xchgeaxeax90/wisp-nametag/src_avr/animation.c

#include "animation.h"
#include <avr/interrupt.h>
#include <avr/io.h>

#include "animation_circle.inc"
#include "animation_breathe.inc"
#include "animation_wave.inc"
#include "animation_blink.inc"
#include "animation_twinkle.inc"
#include "animation_on.inc"

const __flash animation_data_t animation_off[] = {
    {{ 0, 0, 0, 0, 0, 0, 0, 0, 0, 0}, .timeout = 10}
};

const __flash animation_data_t* animation_array[] = {
    animation_circle,
    animation_twinkle,
    animation_breathe,
    animation_wave,
    animation_blink,
    animation_on,
    animation_off
};
const uint8_t max_animation_select = 5;


const __flash uint8_t animation_sizes[] = {
    sizeof(animation_circle)/sizeof(animation_circle[0]),
    sizeof(animation_twinkle)/sizeof(animation_twinkle[0]),
    sizeof(animation_breathe)/sizeof(animation_breathe[0]),
    sizeof(animation_wave)/sizeof(animation_wave[0]),
    sizeof(animation_blink)/sizeof(animation_blink[0]),
    sizeof(animation_on)/sizeof(animation_on[0]),
    sizeof(animation_off)/sizeof(animation_off[0]),
};

const __flash animation_data_t *animation_ptr = &animation_circle[0];

uint16_t timeout_counter = 0;
uint8_t animation_idx = 0;
uint8_t selected_animation = 0;
uint8_t update_animation(void){
    if(timeout_counter >= animation_ptr->timeout){
        timeout_counter = 0;
        animation_idx += 1;
        if(animation_idx >= animation_sizes[selected_animation]){
            animation_idx = 0;
        }
        cli();
        animation_ptr = &animation_array[selected_animation][animation_idx];
        sei();
        return 1;
    } else {
	timeout_counter = timeout_counter + 1;
	return 0;
    }
}

void select_animation(void){
    cli();
    selected_animation += 1;
    if(selected_animation >= max_animation_select){
	selected_animation = 0;
    }
    animation_idx = 0;
    timeout_counter = 0;
    sei();
}

void select_on_animation(void){
    cli();
    selected_animation = max_animation_select;
    animation_idx = 0;
    timeout_counter = 0;
    sei();
}

void select_off_animation(void){
    cli();
    selected_animation = max_animation_select+1;
    animation_idx = 0;
    timeout_counter = 0;
    sei();
}
