xchgeaxeax90/wisp-nametag/src/animation.h

#pragma once
#include "fw_hal.h"
#include "pwm.h"

typedef struct {
    pwm_settings_t pwm_settings;
    uint16_t timeout;
} animation_data_t;

extern const __CODE animation_data_t *animation_ptr;

__BIT update_animation(void);

void select_animation(void);
void select_on_animation(void);
void select_off_animation(void);
